gitzense/bot/photos and videos/bot_2.jpg

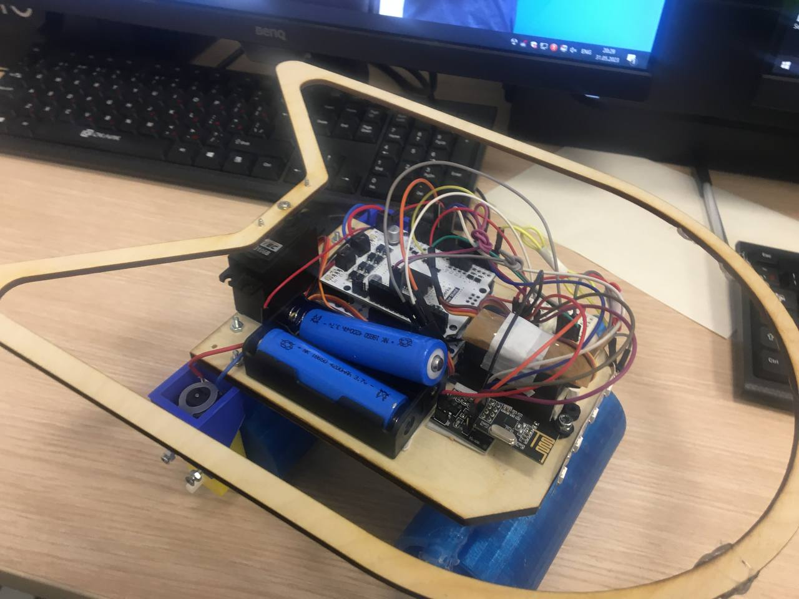
photos and videos/bot_2.jpg
