gitzense/bot/photos and videos/bot_4.jpg

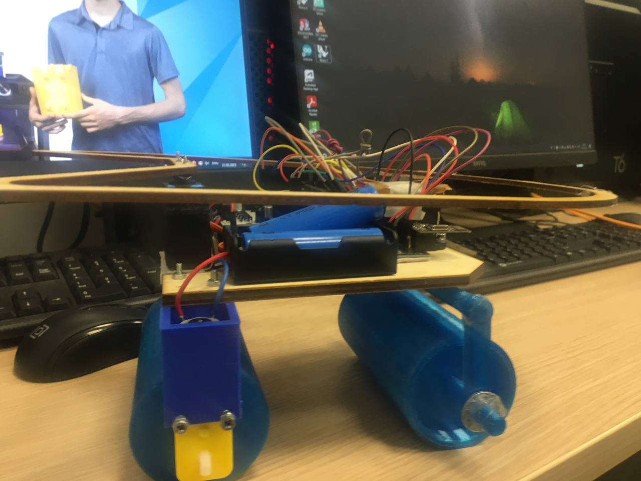
photos and videos/bot_4.jpg
