gitzense/bot/photos and videos/bot_6.jpg

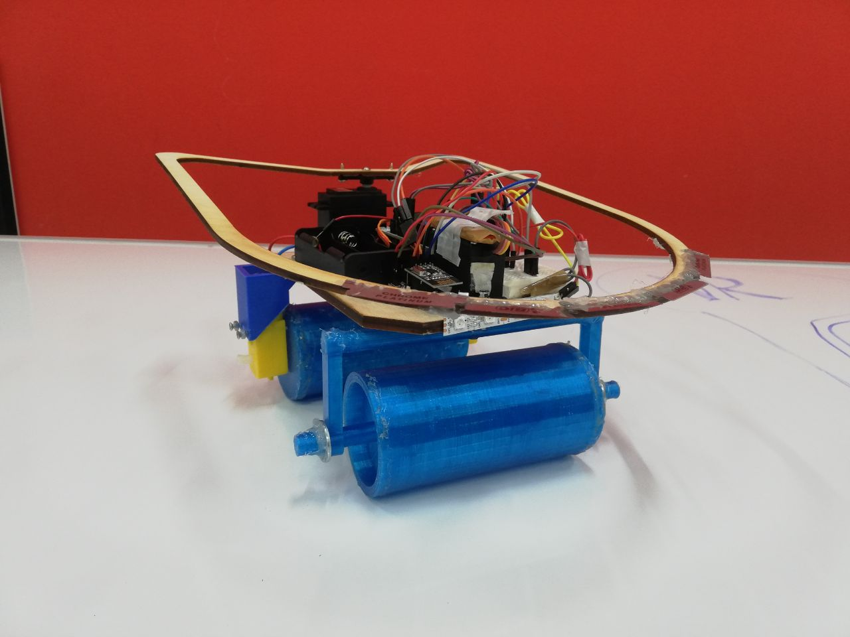
photos and videos/bot_6.jpg
