gitzense/bot/photos and videos/controller.jpg

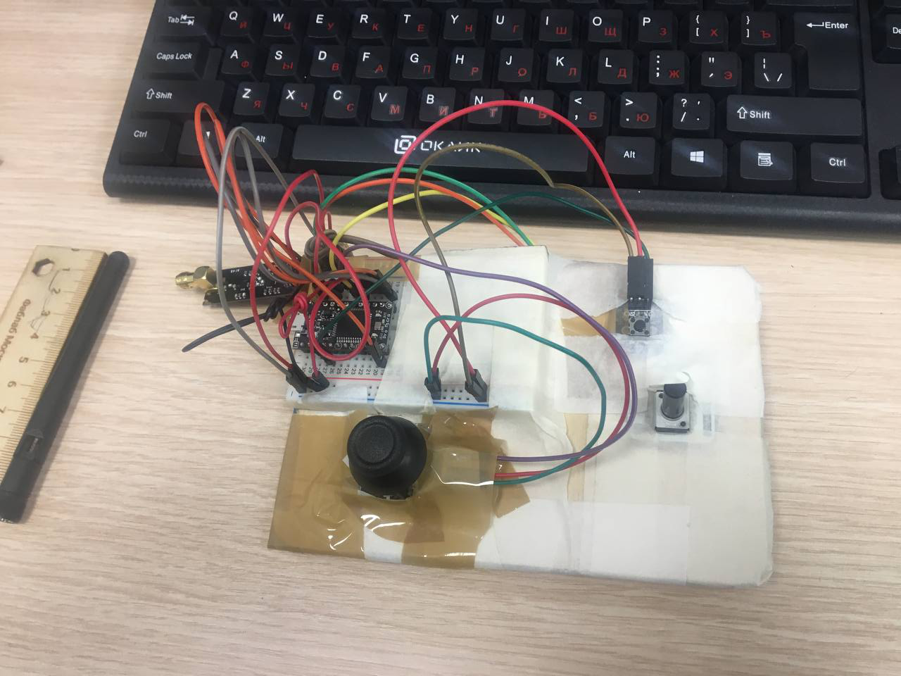
photos and videos/controller.jpg
